svilches/kom/hw/brd/blocks/encoder/encoder.png

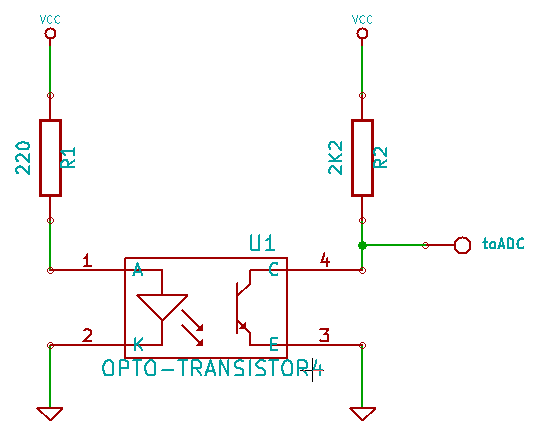
hw/brd/blocks/encoder/encoder.png
