svilches/kom/hw/brd/blocks/power/pwrMgt.png

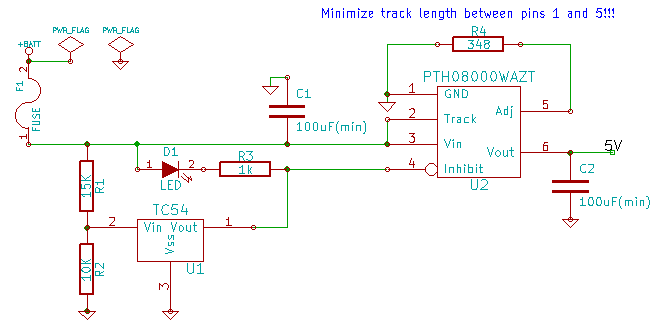
hw/brd/blocks/power/pwrMgt.png
