svilches/kom/hw/brd/blocks/xbee/interferences.png

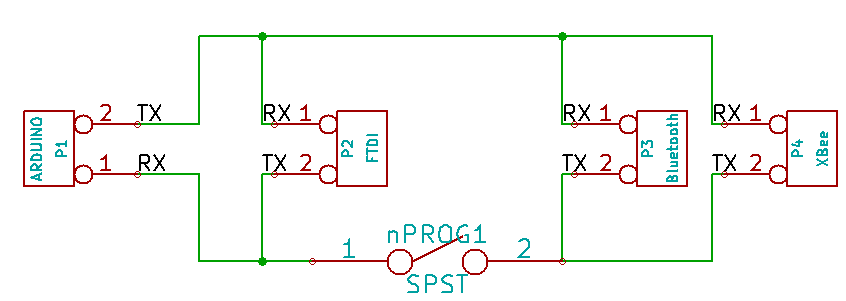
hw/brd/blocks/xbee/interferences.png
