svilches/kom/hw/brd/blocks/xbee/xbee_receiver.png

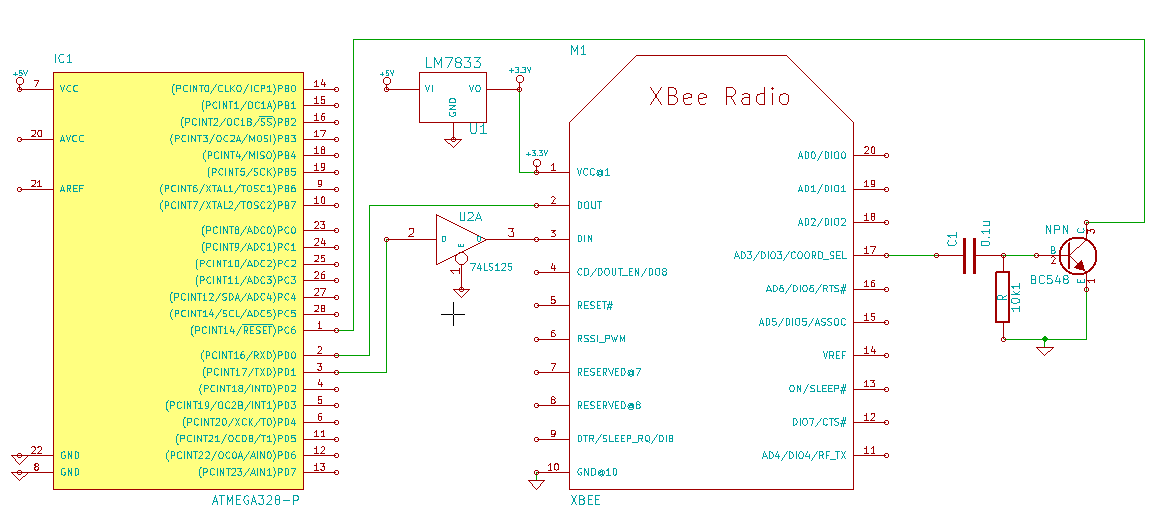
hw/brd/blocks/xbee/xbee_receiver.png
