svilches/kom/hw/brd/blocks/xbee/xbee_transmitter.png

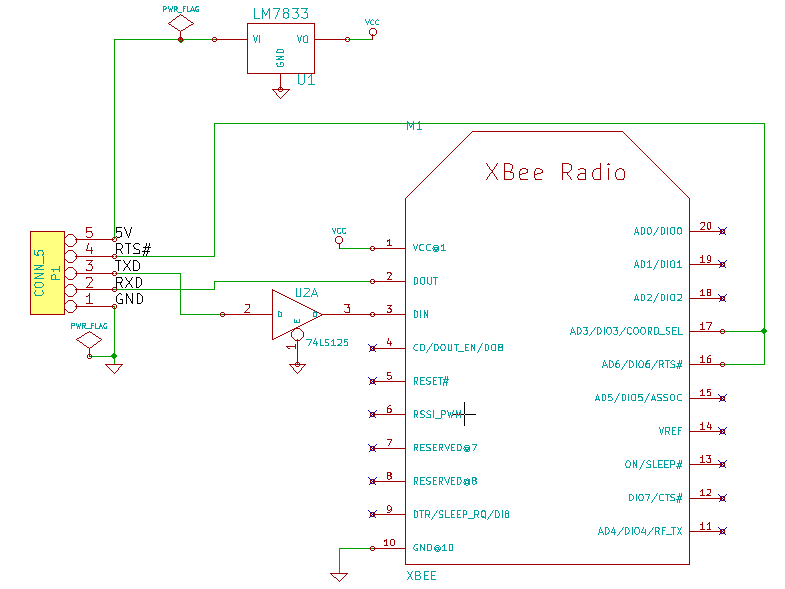
hw/brd/blocks/xbee/xbee_transmitter.png
