svilches/kom/hw/doc/datasheets/buffer_pins.png

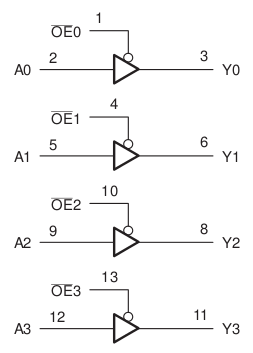
hw/doc/datasheets/buffer_pins.png
