svilches/kom/hw/doc/datasheets/CD4067.png

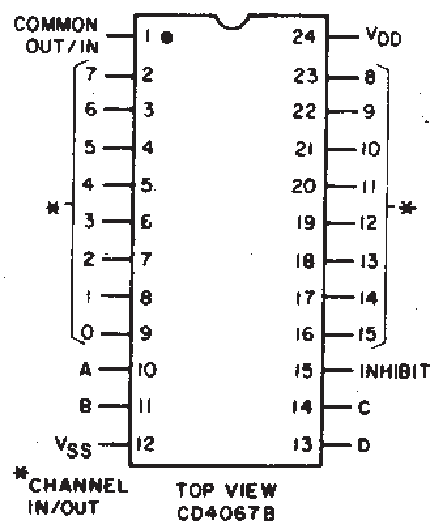
hw/doc/datasheets/CD4067.png
