svilches/kom/hw/doc/datasheets/CD4097_pins.png

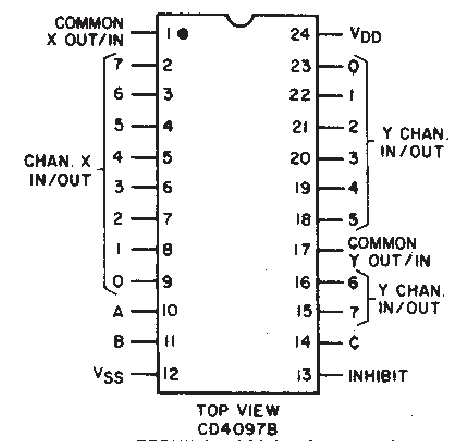
hw/doc/datasheets/CD4097_pins.png
