svilches/kom/hw/doc/datasheets/CD40106_Pins.png

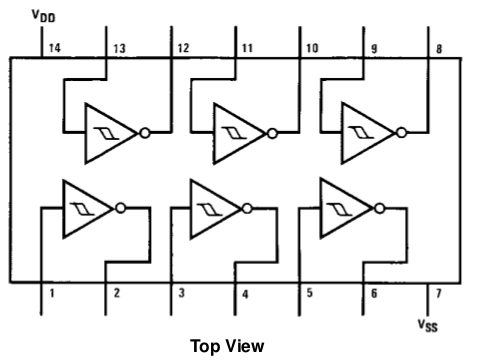
hw/doc/datasheets/CD40106_Pins.png
