svilches/kom/hw/doc/datasheets/L293.png

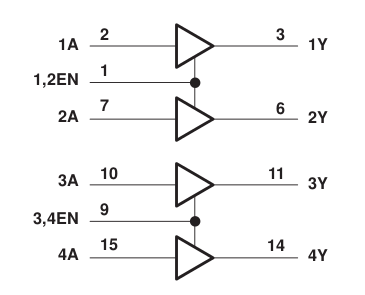
hw/doc/datasheets/L293.png
