svilches/kom/hw/doc/datasheets/LM311_functional.png

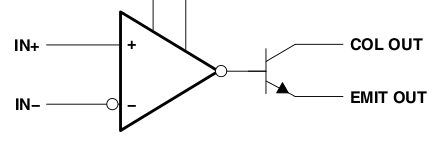
hw/doc/datasheets/LM311_functional.png
