svilches/kom/hw/doc/datasheets/MotoReductor_resumen.jpg

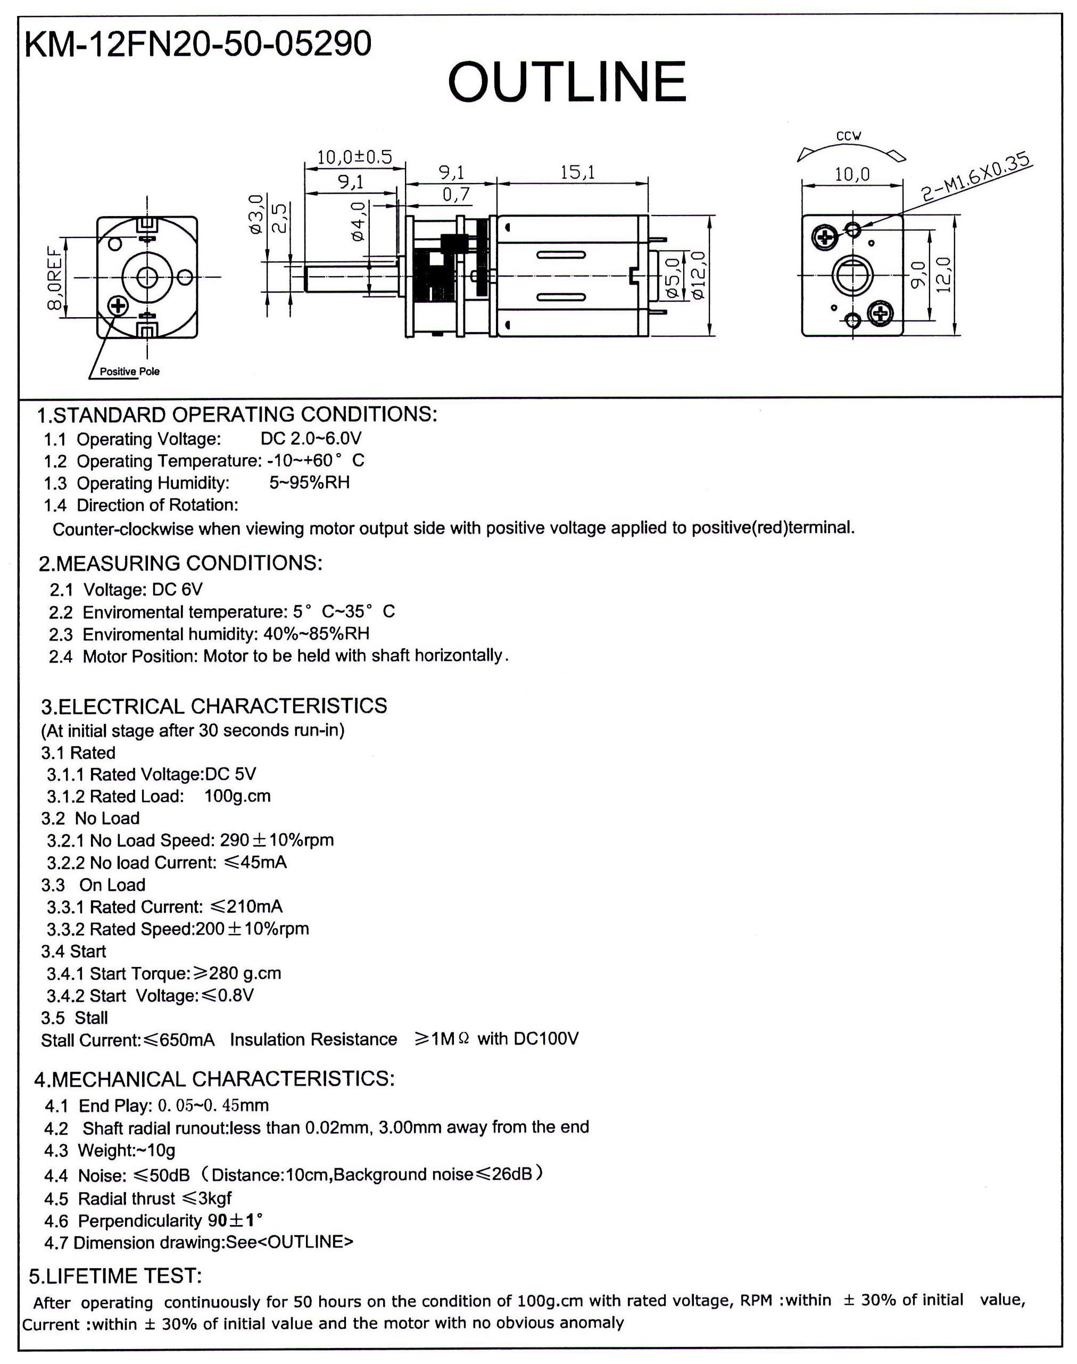
hw/doc/datasheets/MotoReductor_resumen.jpg
