svilches/kom/hw/doc/datasheets/PT480F_Pins.png

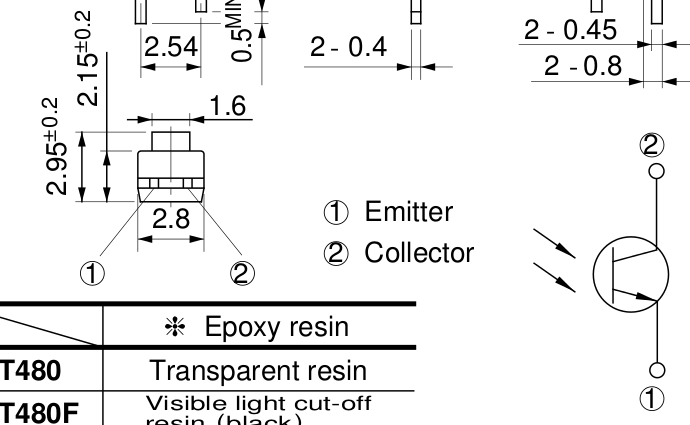
hw/doc/datasheets/PT480F_Pins.png
