svilches/kom/hw/doc/efficiency_PTH08000W.png

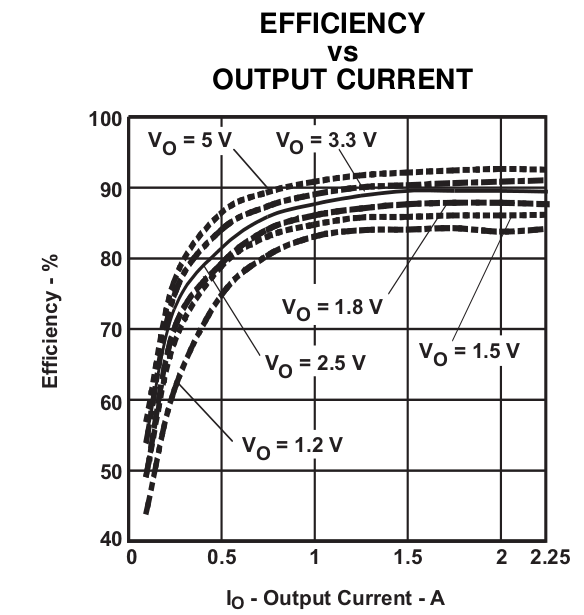
hw/doc/efficiency_PTH08000W.png
