svilches/kom/hw/doc/oscope/NewFile3.bmp

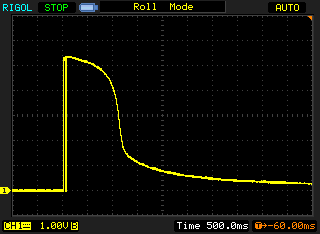
hw/doc/oscope/NewFile3.bmp
