svilches/kom/hw/fab/postscript/kom-Back.pdf

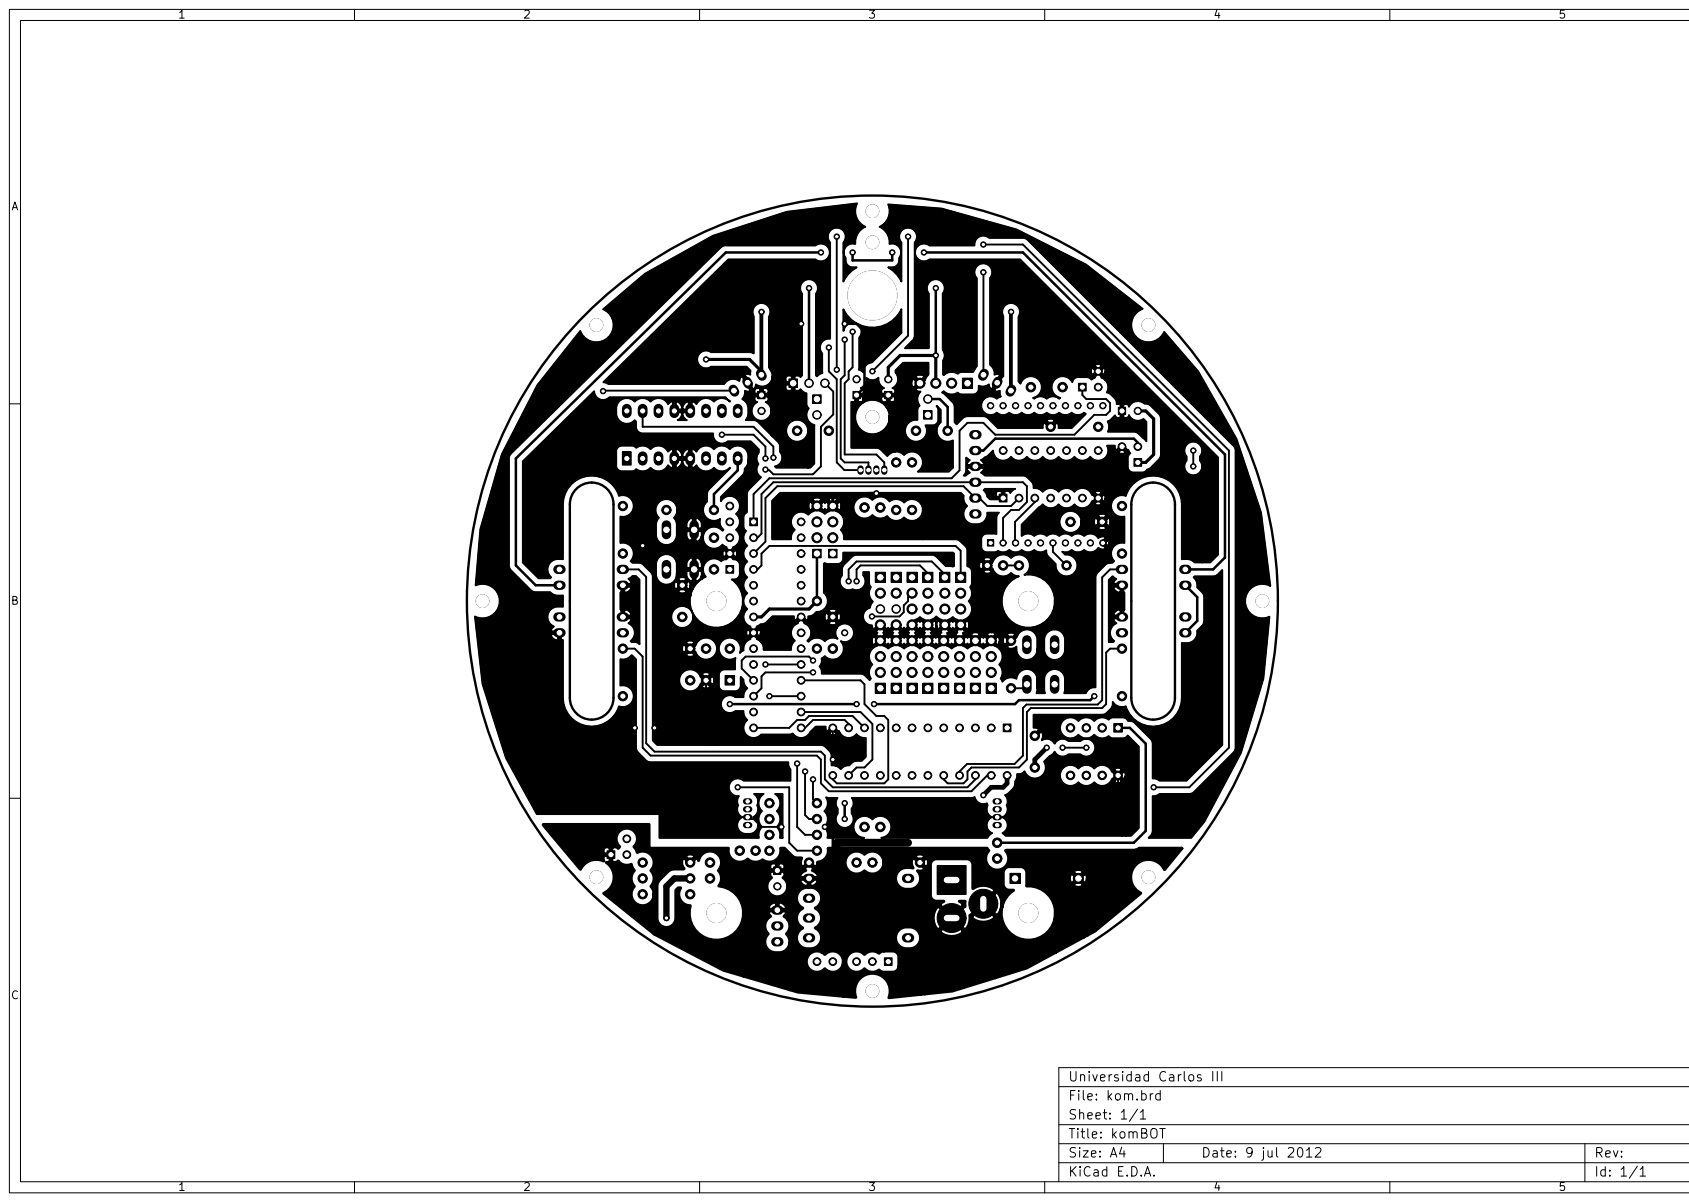
[picture p42: page 1]
