svilches/kom/hw/fab/postscript/kom-Front.pdf

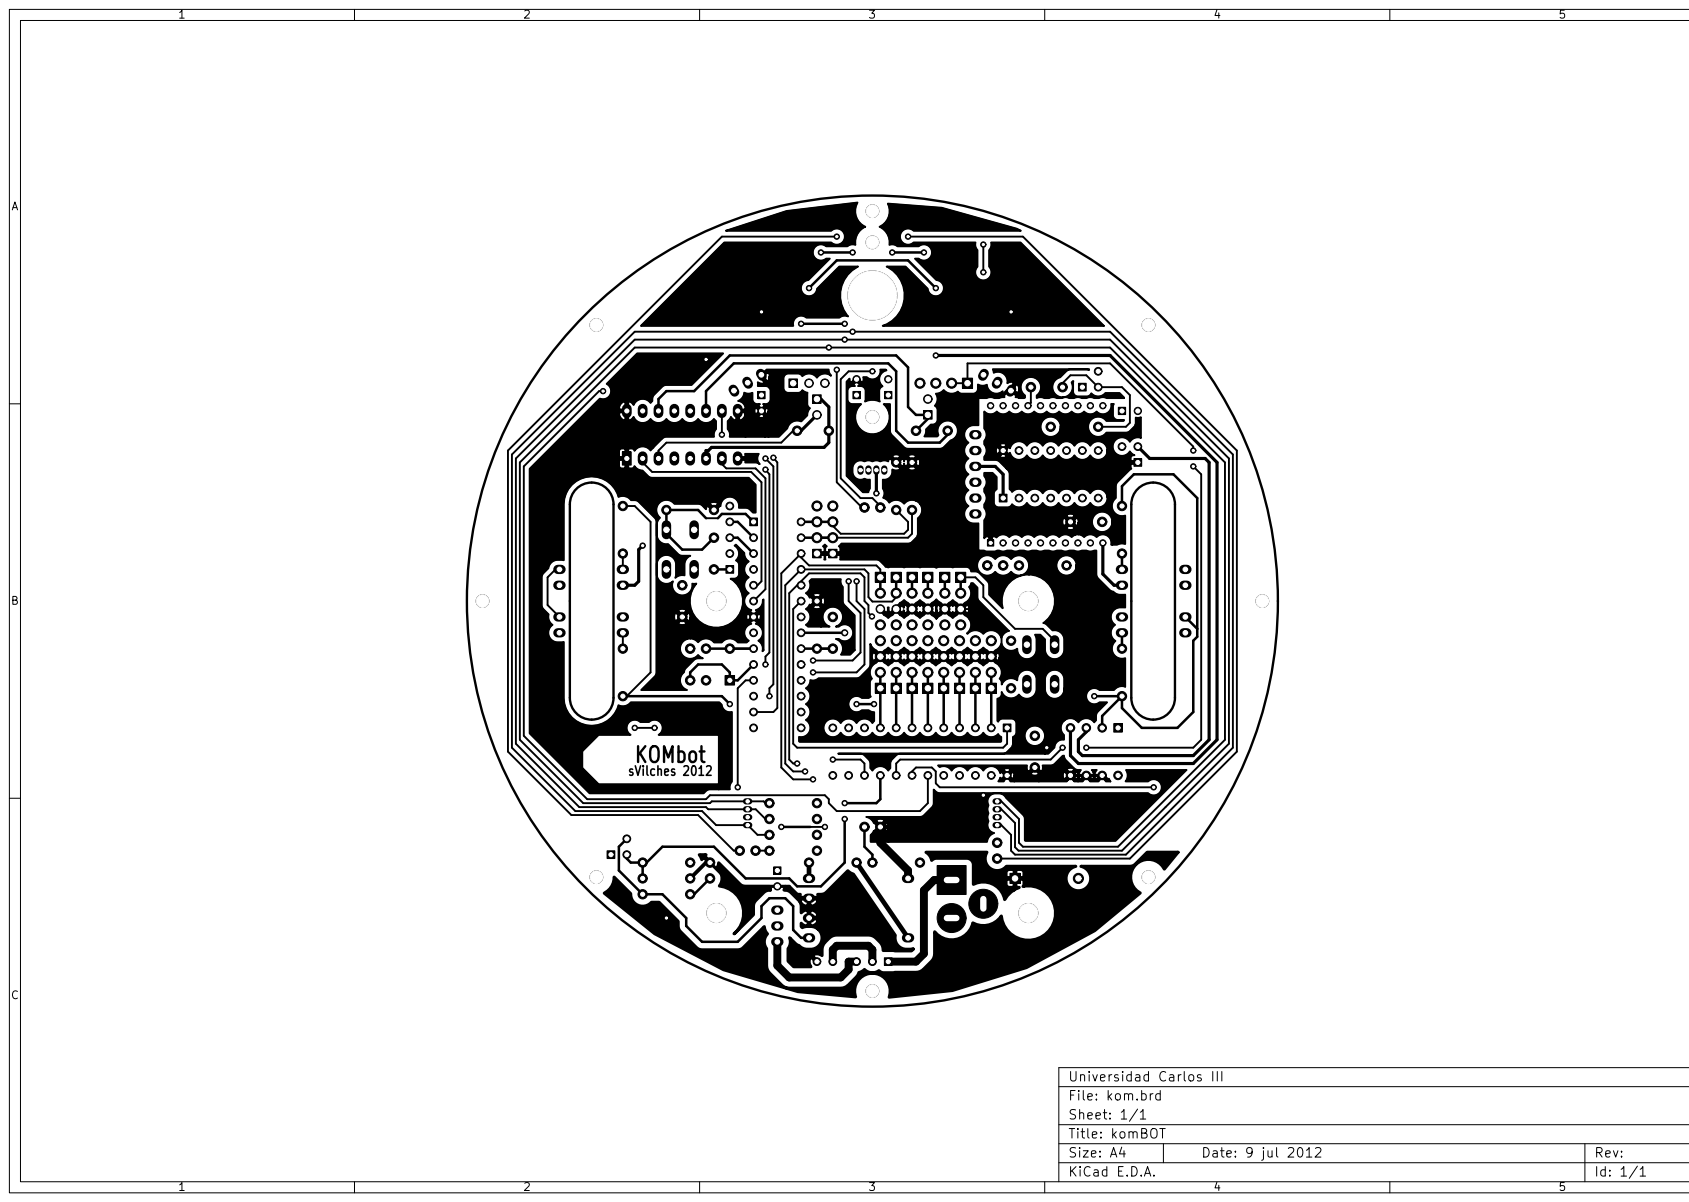
[picture p43: page 1]
