svilches/kom/hw/fab/postscript/kom-SilkS_Front.pdf

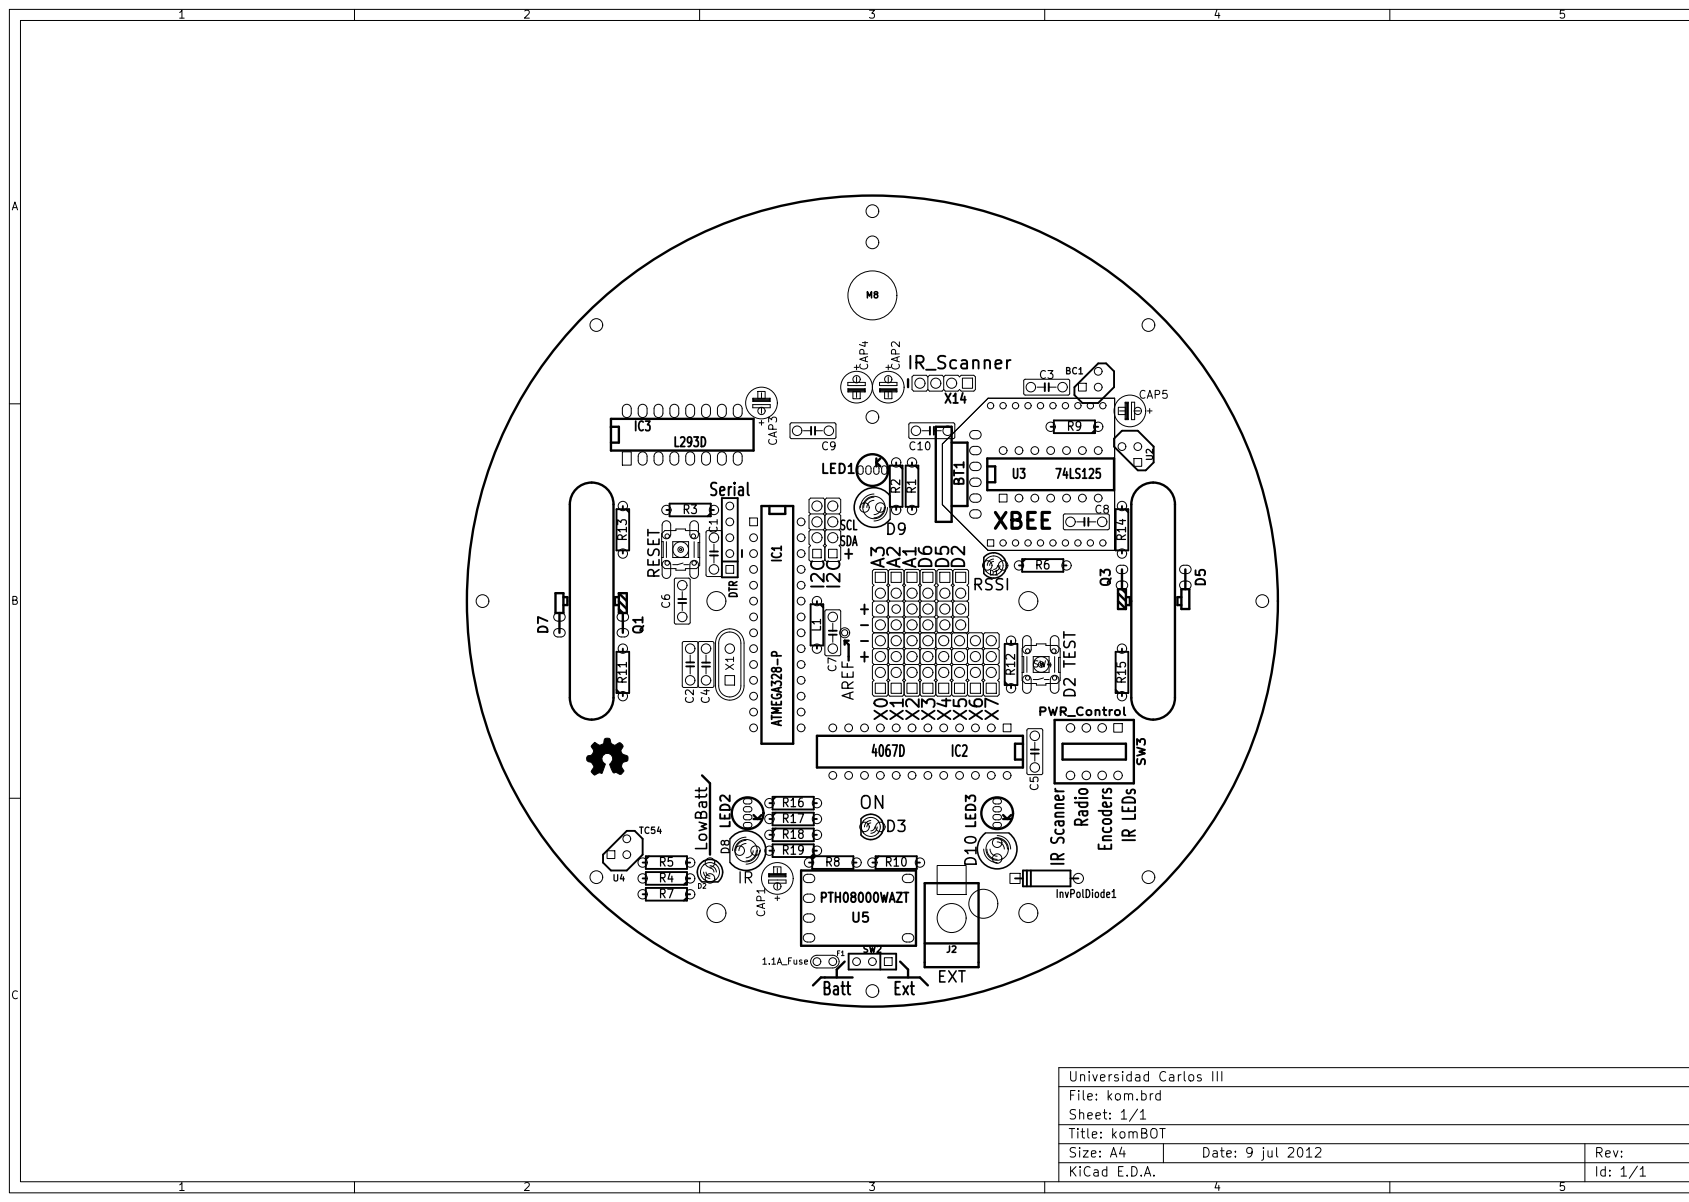
[picture p44: page 1]
