svilches/kom/hw/fab/postscript/kom-SilkS_Back.pdf

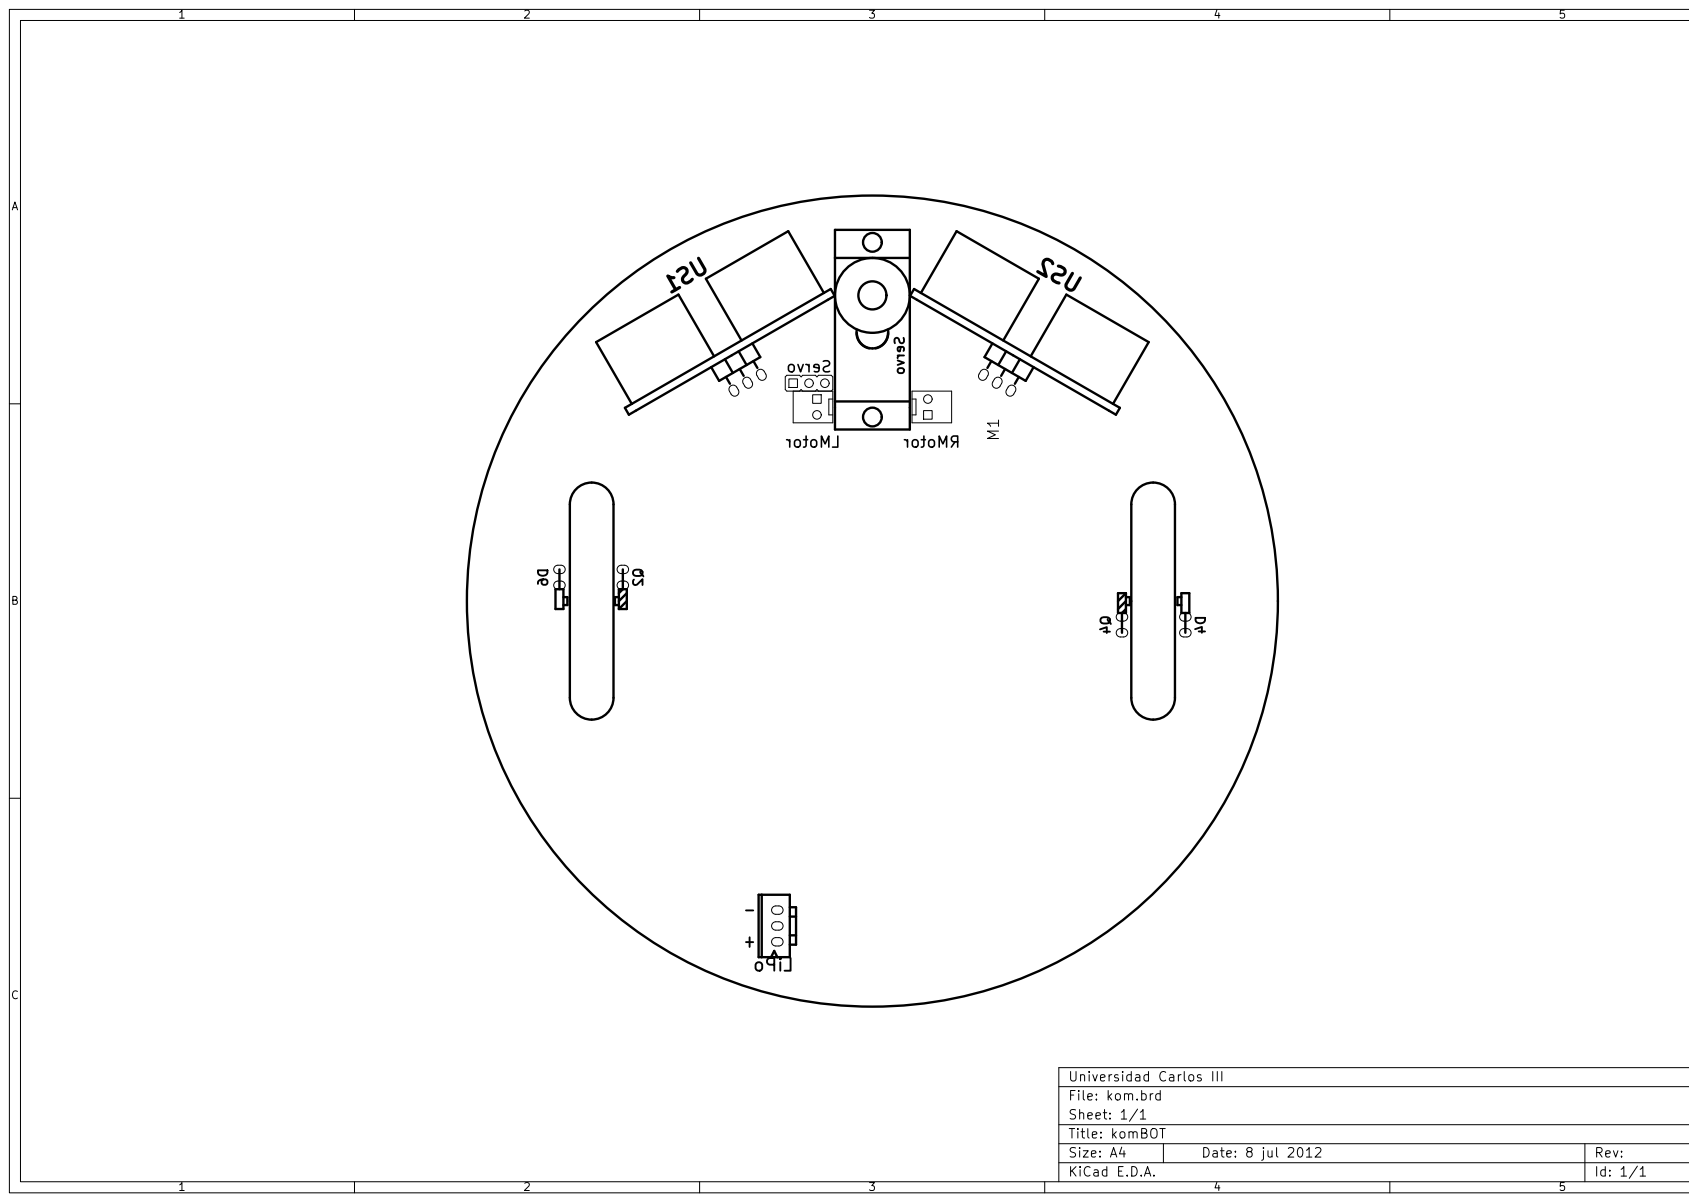
[picture p45: page 1]
