svilches/kom/hw/fab/forFab/PDFs/kom-Back.pdf

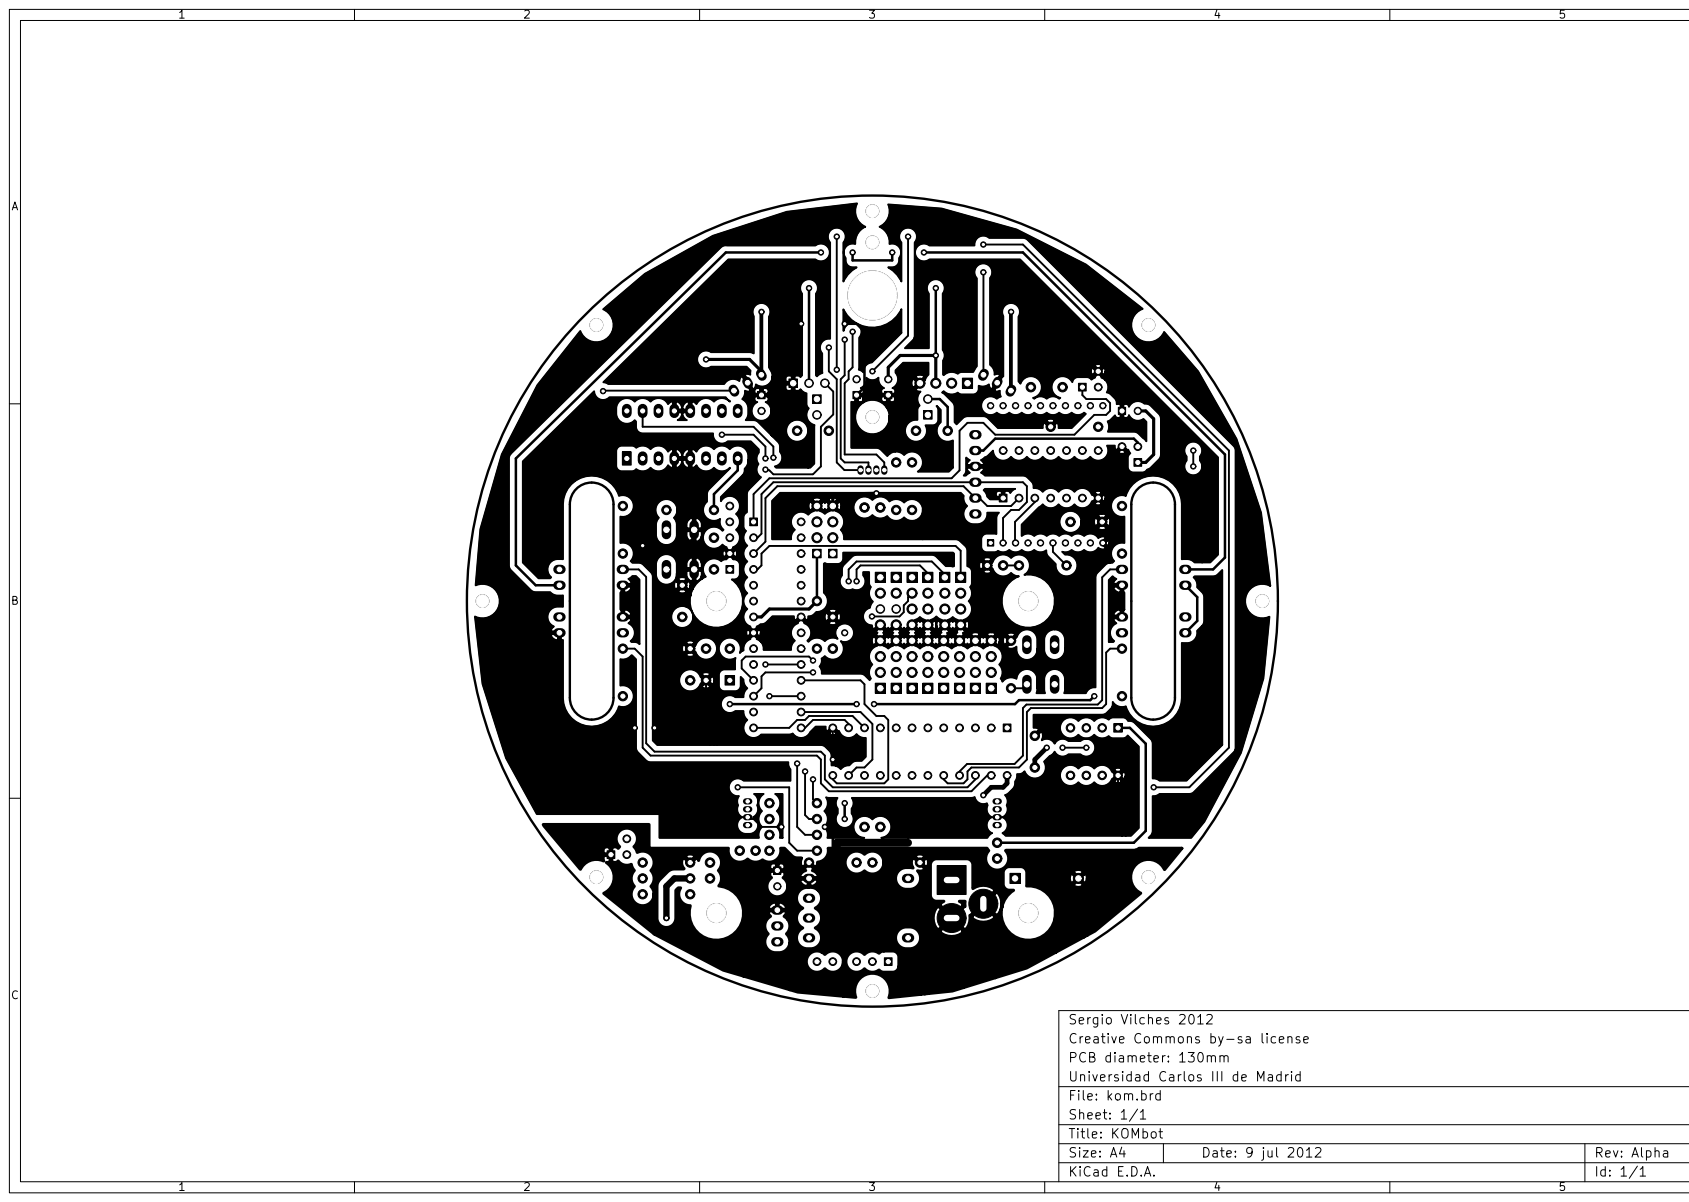
[picture p46: page 1]
