svilches/kom/hw/fab/forFab/PDFs/kom-Front.pdf

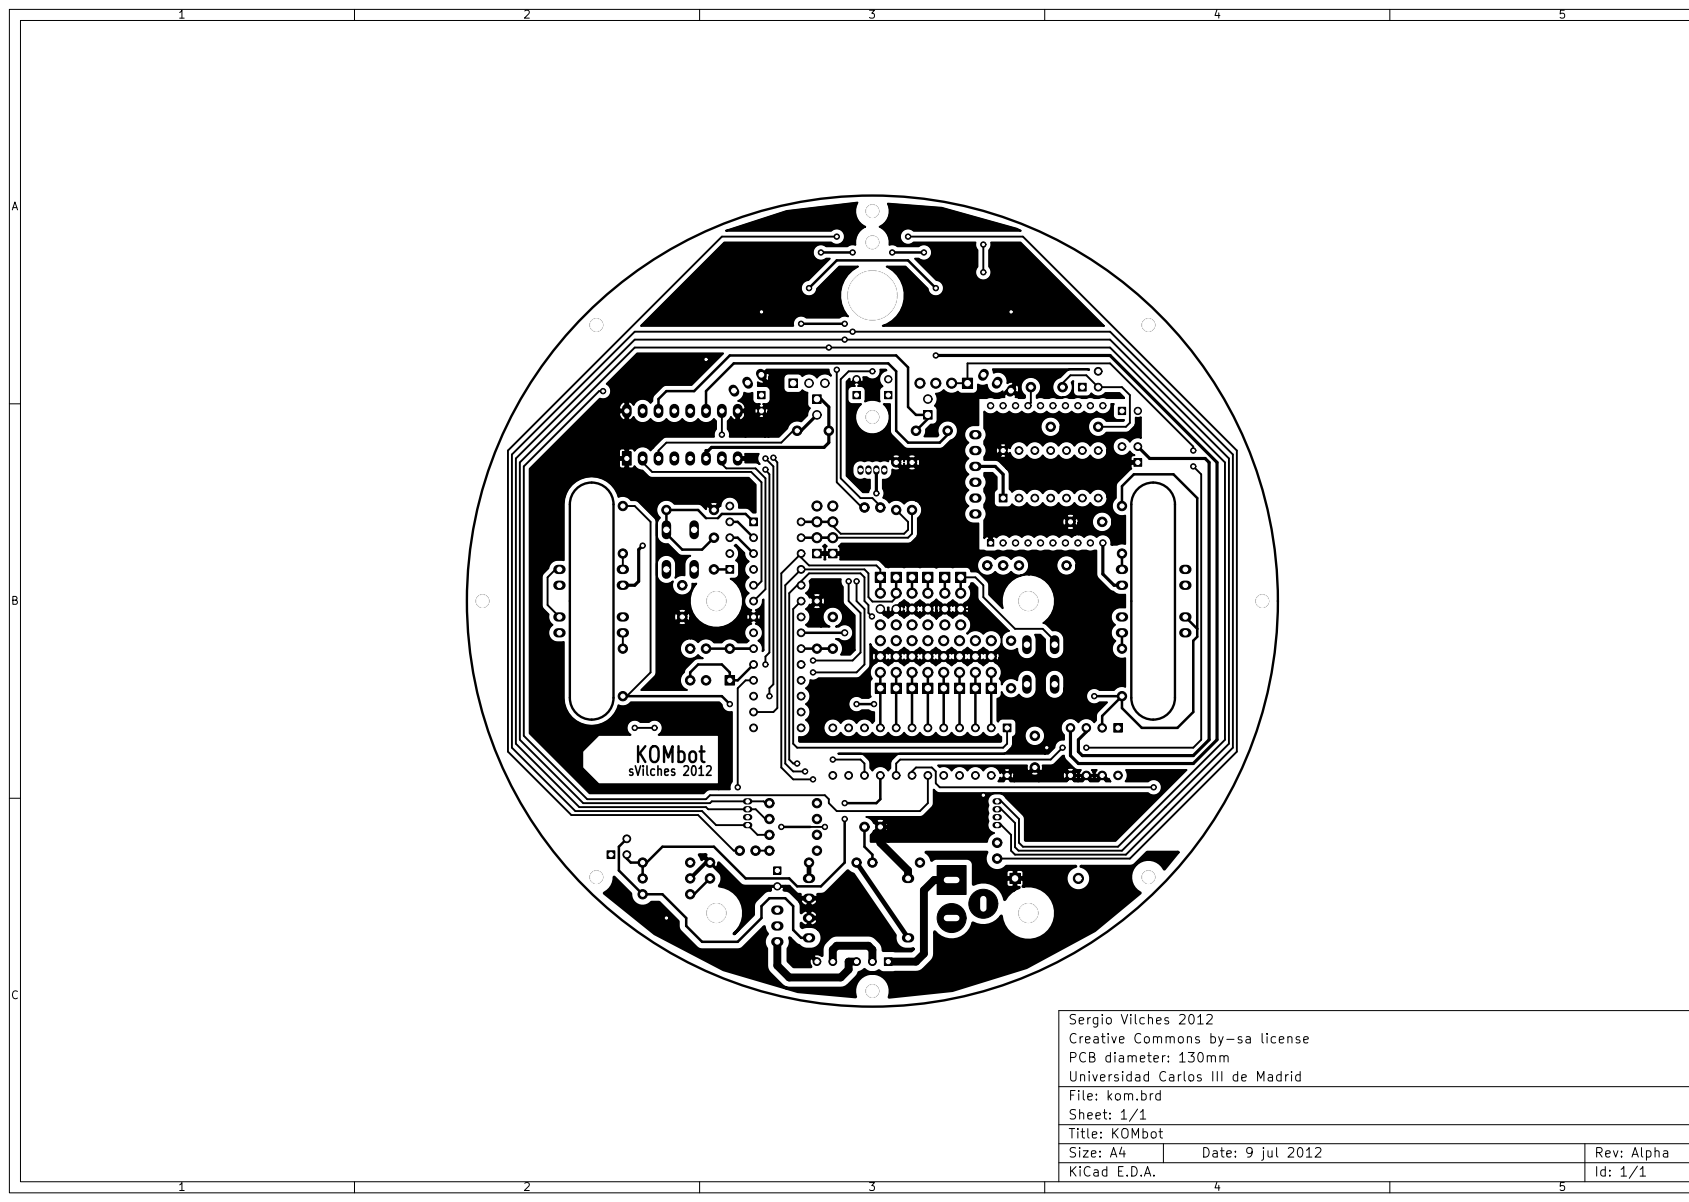
[picture p47: page 1]
