svilches/kom/hw/fab/forFab/PDFs/kom-SilkS_Back.pdf

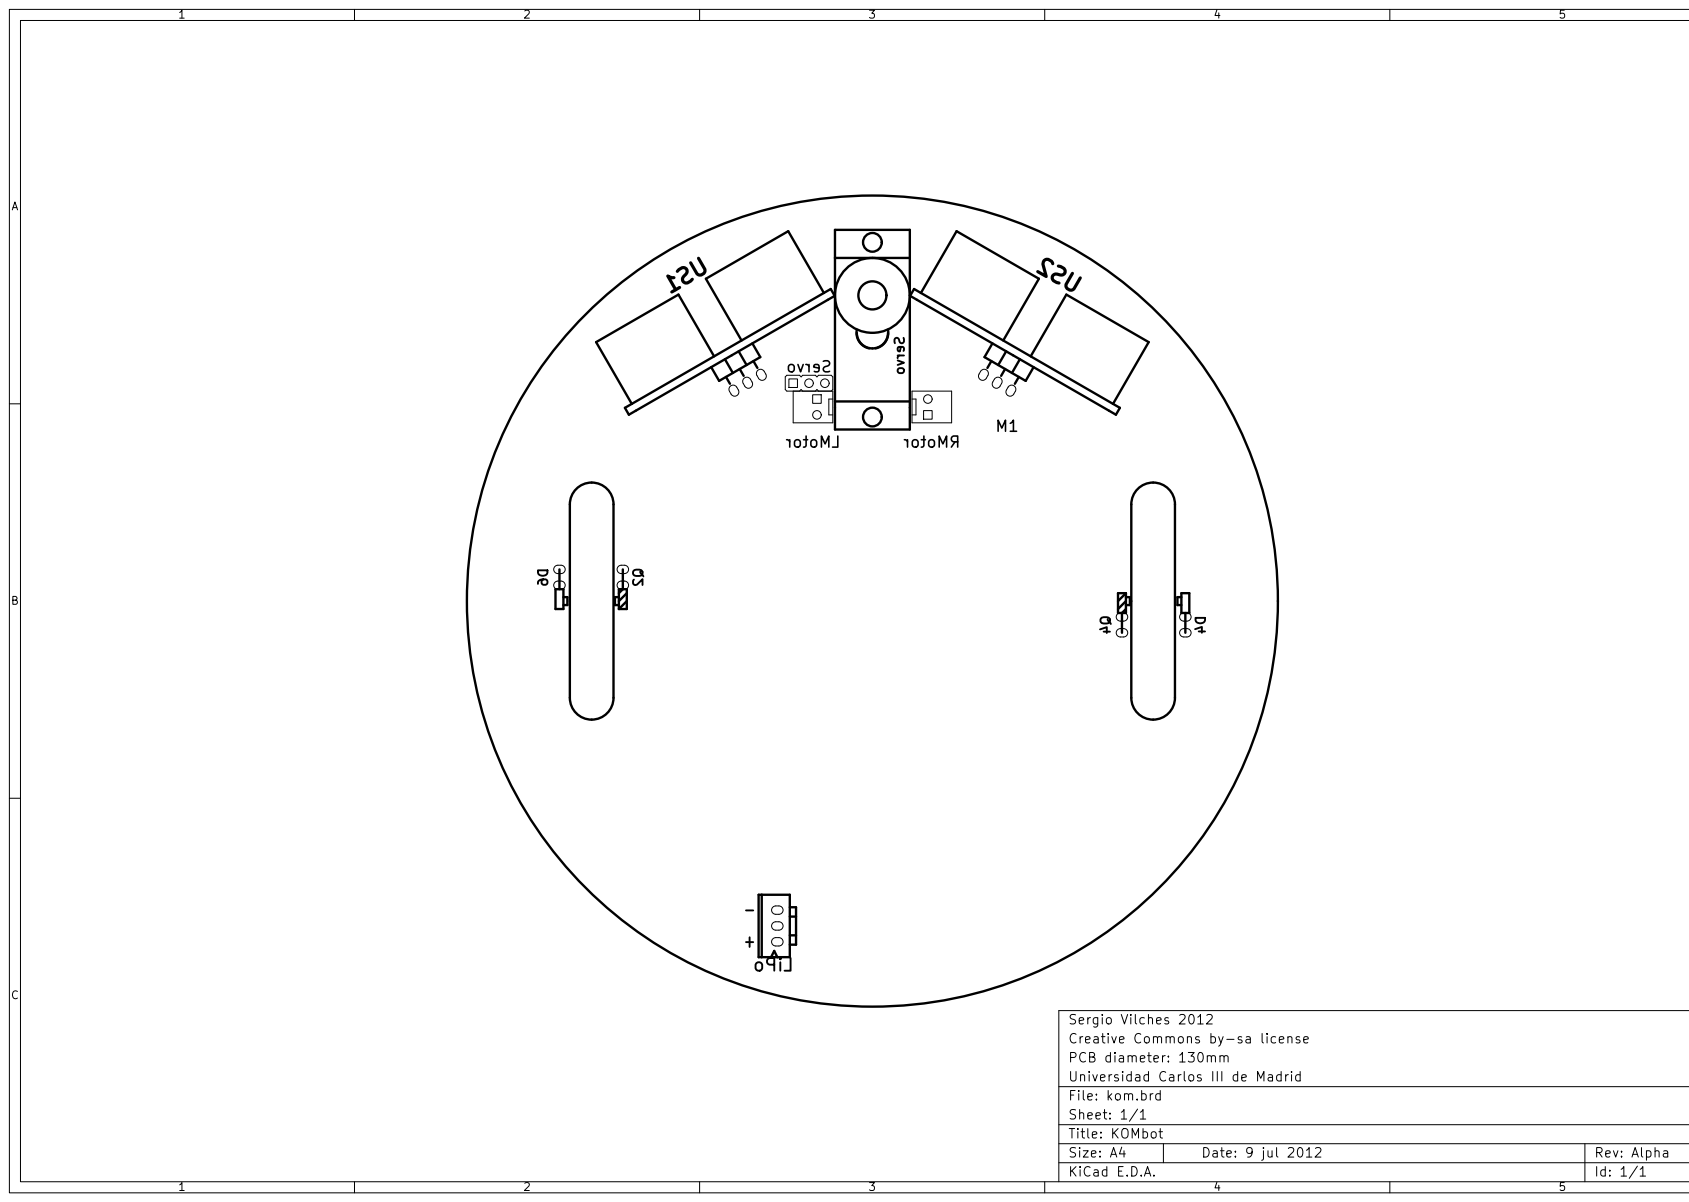
[picture p48: page 1]
