svilches/kom/hw/fab/forFab/PDFs/kom-SilkS_Front.pdf

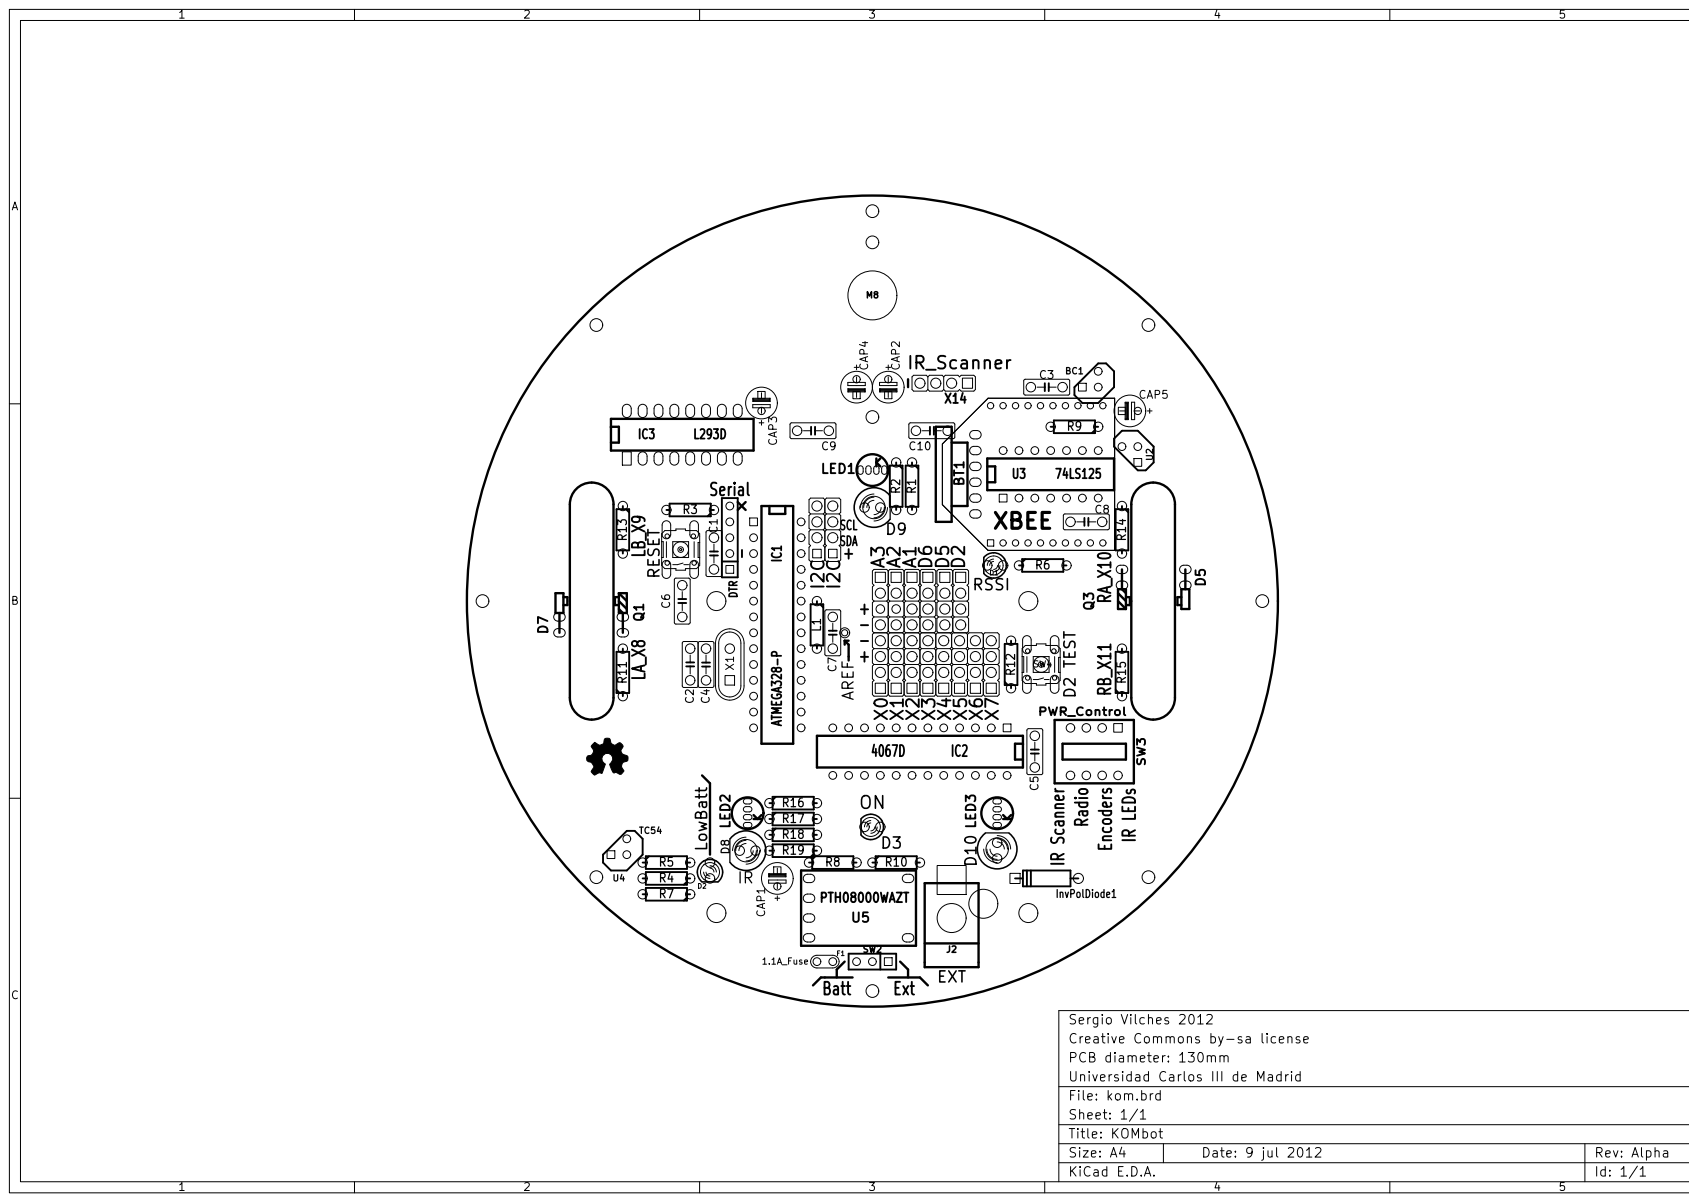
[picture p49: page 1]
