svilches/kom/hw/brd/kom.sch

## KiCad design hw/brd/kom.sch (2012-08-25)

Schematic: kom.sch

Parts:
BC1: BC547
BT1: BLUETOOTHMOD_DX
C1: 100nF
C2, C4: 22pF
C3: 0.1u
C5: 100n MUX
C6: 100n AVR
C7: 100n AVCC
C8: 8.2pF Radio
C9: 100nF MotorL
C10: 100nF MotorR
CAP1: 100uF InCap
CAP2: 10uF IR
CAP3: 100uF HBridge
CAP4: 10uF US
CAP5: 1uF Radio
CP1: LMotor
CP2: RMotor
D1: RSSI
D2: UVLO
D3: ON
D4, D5, D6, D7: IR_LED
D8, D9, D10: IR_LD271
D11: 5.1V
F1: 1.1A Fuse
I1, I2: I2C
IC1: ATMEGA328-P; DIL28
IC2: 4067D; 40xx-SO24W
IC3: L293D; stepper drivers-DIL16
InvPolDiode1: 200mA IPP
J1: LiPo
J2: EXT
JP1: ServoScanner
K1: 3V3 Serial
LED1, LED2, LED3: LED_RCGB
M1: XBEE; xbee_r1-XBEE
P1: Serial
P2: ARef
P3: D2
P4: D5
P5: D6
P6: A1
P7: A2
P8: A3
P9: IR_Scanner
P10: X0
P11: X1
P12: X2
P13: X3
P14: X4
P15: X5
P16: X6
P17: X7
Q1, Q2, Q3, Q4: PT480F
R1, R2: 1.5K
R3, R5, R9: 10K
R4: 15K
R6, R16, R17: 220
R7: 1k
R8: 348
R10: 330
R11, R13, R14, R15: 2.2K
R12: 500
R18: 180
SW1: SW_RESET
SW2: PwrOn
SW4: TEST
U1: 10uH
U2: MCP1700-3302E
U3: 74LS125
U4: TC54
U5: PTH08000WAZT
US1: US_L
US2: US_R
X1: 16MHz

Notes on the sheet:
Minimize track length between pins 1 and 5!!!
Check Polarity of connectors!!
Power Supply and Management
Communications
Serial
I2C
Bluetooth
Microcontroller Core
Motor Control and Encoders
Outputs: RGB and IR
Sensors
Each color of each LED carries 5mA
Limiting Resistor
PWM
GPIOs
Decoupling Capacitors
3.3V Serial
