svilches/kom/hw/brd/blocks/encoder/encoder.sch

## KiCad design hw/brd/blocks/encoder/encoder.sch (2012-06-18)

Schematic: encoder.sch

Parts:
R1: 220
R2: 2K2
U1: OPTO-TRANSISTOR4
toADC: CONN_1
