svilches/kom/hw/brd/blocks/power/pwrProtection.sch

## KiCad design hw/brd/blocks/power/pwrProtection.sch (2012-06-18)

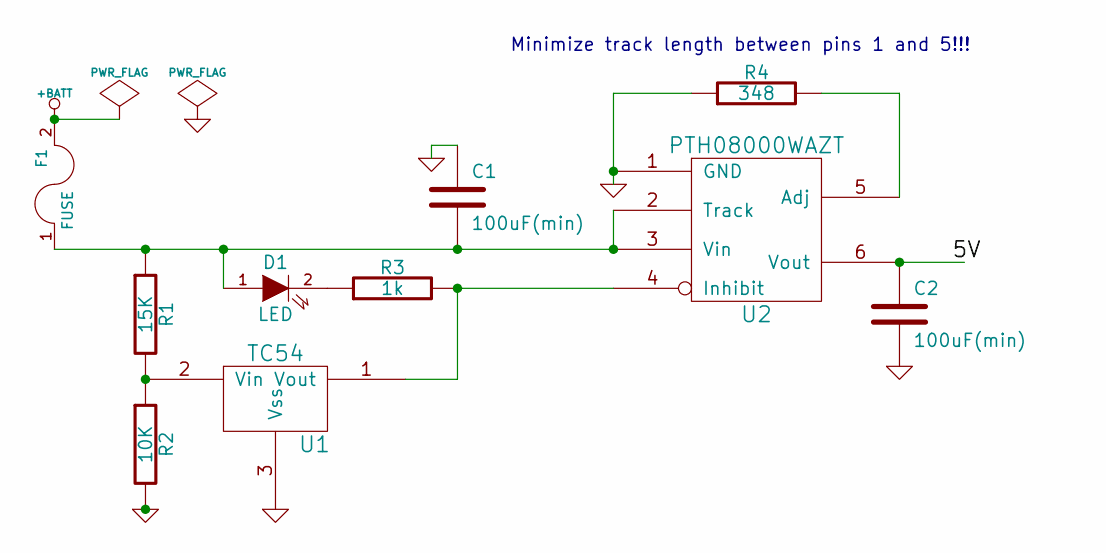
[picture p50: schematic pwrProtection.sch]

Parts:
C1, C2: 100uF(min)
D1: LED
F1: FUSE
R1: 15K
R2: 10K
R3: 1k
R4: 348
U1: TC54
U2: PTH08000WAZT

Connections:
5V: C2.1, U2.6 (Vout)
+BATT: F1.2
GND: C1.1, C2.2, R2.2, R4.1, U1.3 (Vss), U2.1 (GND)
unnamed: C1.2, D1.1 (A), F1.1, R1.1, U2.2 (Track), U2.3 (Vin)
unnamed: D1.2 (K), R3.1
unnamed: R1.2, R2.1, U1.2 (Vin)
unnamed: R3.2, U1.1 (Vout), U2.4 (Inhibit)
unnamed: R4.2, U2.5 (Adj)

Notes on the sheet:
Minimize track length between pins 1 and 5!!!
