svilches/kom/hw/brd/blocks/xbee/$noname.sch

## KiCad design hw/brd/blocks/xbee/$noname.sch (2012-06-18)

Schematic: $noname.sch

Parts:
10k1: R
BC548: NPN
C1: 0.1u
IC1: ATMEGA328-P; DIL28
M1: XBEE; xbee_r1-XBEE
U1: LM7833
U2: 74LS125
