svilches/kom/hw/brd/blocks/xbee/interferences.sch

## KiCad design hw/brd/blocks/xbee/interferences.sch (2012-06-18)

Schematic: interferences.sch

Parts:
P1: ARDUINO
P2: FTDI
P3: Bluetooth
P4: XBee
nPROG1: SPST
