svilches/kom/hw/brd/blocks/xbee/xbee.sch

## KiCad design hw/brd/blocks/xbee/xbee.sch (2012-06-18)

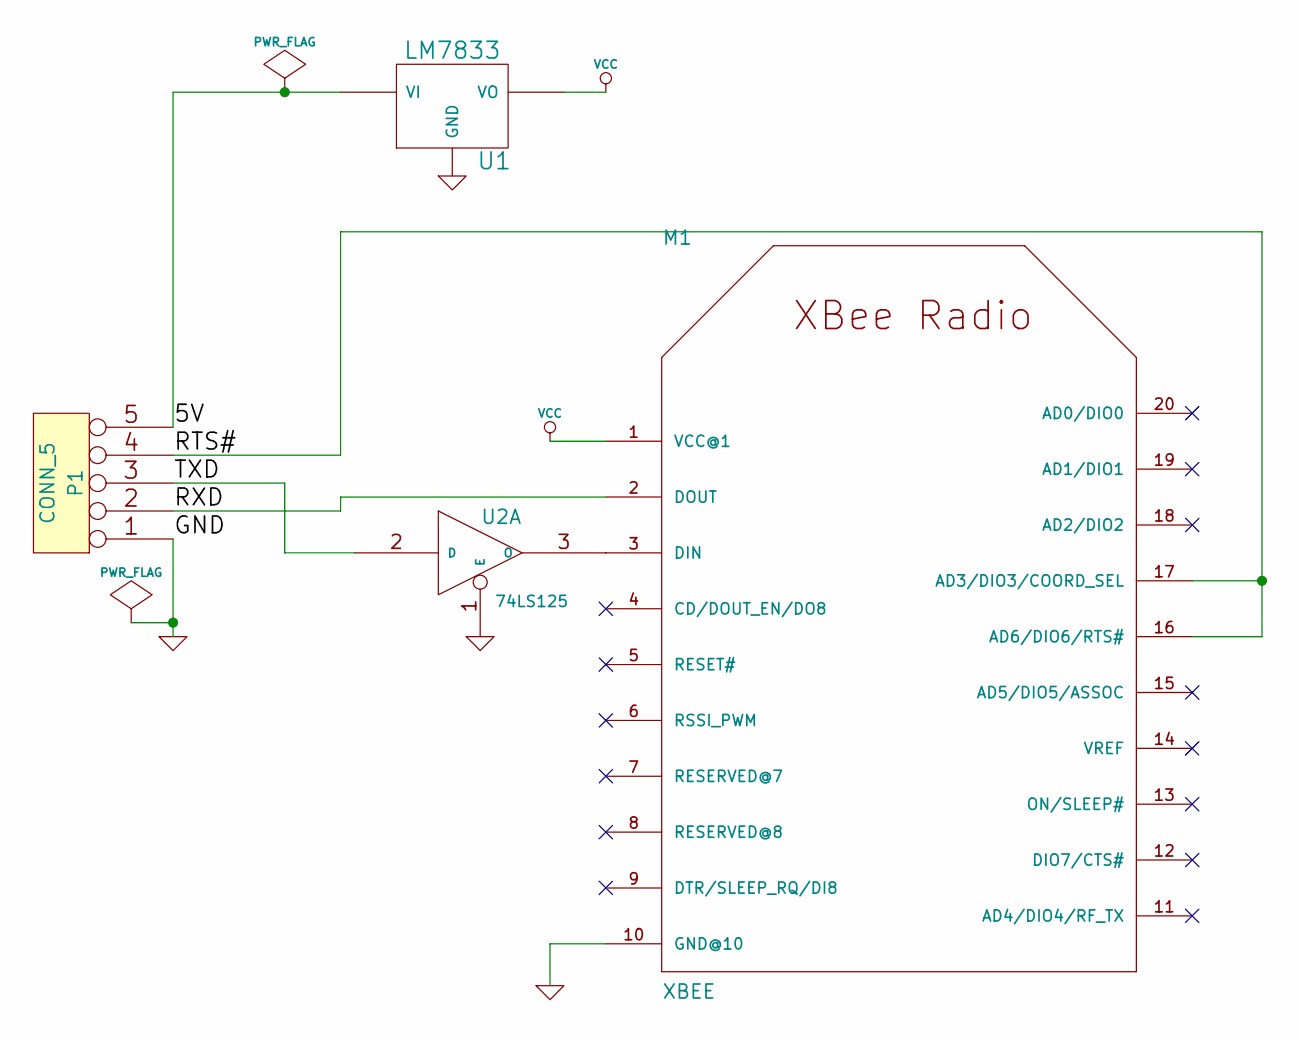
[picture p51: schematic xbee.sch]

Parts:
M1: XBEE; xbee_r1-XBEE
P1: CONN_5
U1: LM7833
U2: 74LS125

Connections:
5V: P1.5, U1.VI
GND: M1.10 (GND@10), P1.1, U1.GND, U2.1 (E)
unnamed: M1.3 (DIN), U2.3 (O)
RTS#: M1.16 (AD6/DIO6/RTS#), M1.17 (AD3/DIO3/COORD_SEL), P1.4
RXD: M1.2 (DOUT), P1.2
TXD: P1.3, U2.2 (D)
VCC: M1.1 (VCC@1), U1.VO
